Robtek-Gruppe-6/semesterproject_4_6/Time_constant_pan.png

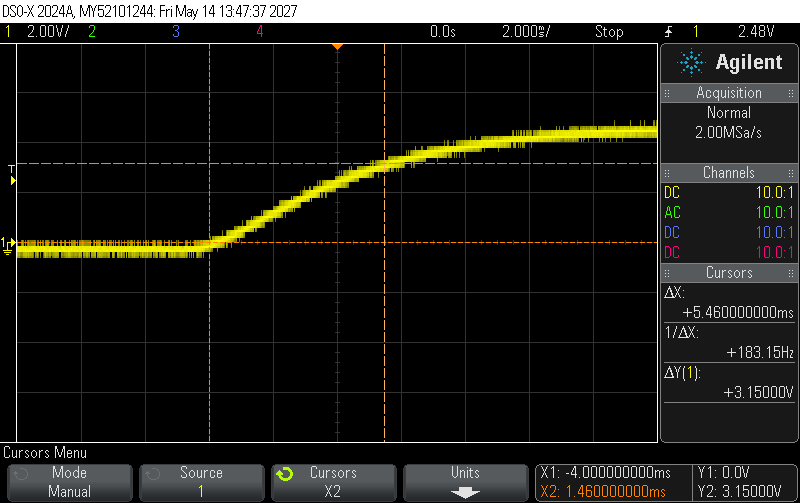
Time_constant_pan.png
