Robtek-Gruppe-6/semesterproject_4_6/Matlab/pid_tests/pan_nopid.png

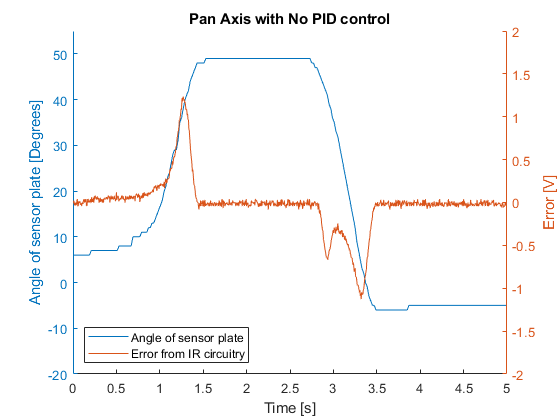
Matlab/pid_tests/pan_nopid.png
