Robtek-Gruppe-6/semesterproject_4_6/Matlab/pid_tests/pan_pid.png

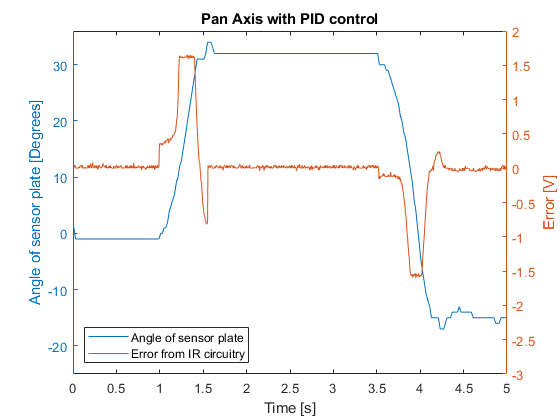
Matlab/pid_tests/pan_pid.png
