Robtek-Gruppe-6/semesterproject_4_6/Matlab/pid_tests/tilt_pid.png

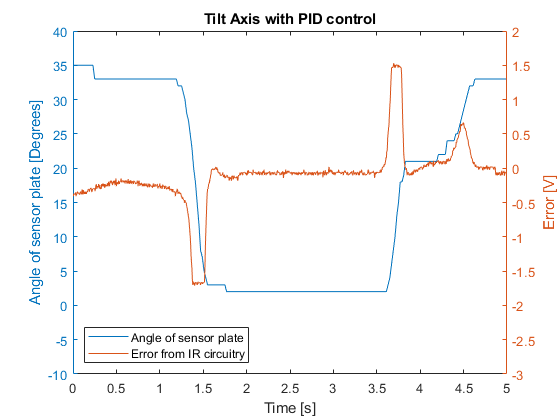
Matlab/pid_tests/tilt_pid.png
