Robtek-Gruppe-6/semesterproject_4_6/Electronics/adder-diff-circuit.kicad_sch

## KiCad design Electronics/adder-diff-circuit.kicad_sch (2025-03-26)

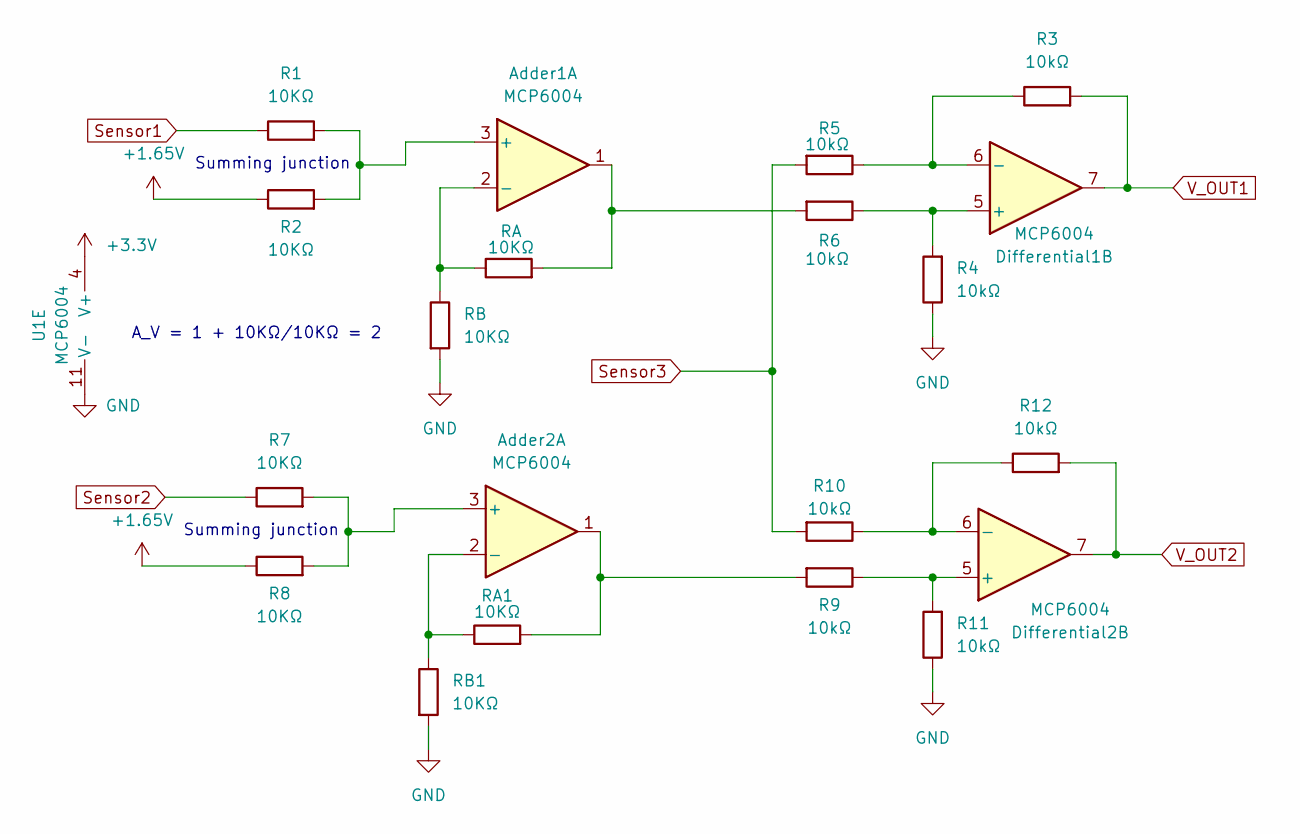
[picture p18: schematic adder-diff-circuit.kicad_sch]

Parts:
Adder1, Adder2: MCP6004
Differential1, Differential2: MCP6004
R1, R2, R7, R8: 10KΩ
R3, R4, R5, R6, R9, R10, R11, R12: 10kΩ
RA, RA1: 10KΩ
RB, RB1: 10KΩ
U1: MCP6004

Connections:
+1.65V: R2.1, R8.1
+3.3V: U1.4 (V+)
GND: R4.1, R11.1, RB.2, RB1.2, U1.11 (V-)
unnamed: Adder1.1, R6.2, RA.2
unnamed: Adder1.2 (-), RA.1, RB.1
unnamed: Adder1.3 (+), R1.2, R2.2
unnamed: Adder2.1, R9.2, RA1.2
unnamed: Adder2.2 (-), RA1.1, RB1.1
unnamed: Adder2.3 (+), R7.2, R8.2
unnamed: Differential1.5 (+), R4.2, R6.1
unnamed: Differential1.6 (-), R3.1, R5.1
unnamed: Differential2.5 (+), R9.1, R11.2
unnamed: Differential2.6 (-), R10.1, R12.1
Sensor1: R1.1
Sensor2: R7.1
Sensor3: R5.2, R10.2
V_OUT1: Differential1.7, R3.2
V_OUT2: Differential2.7, R12.2

Notes on the sheet:
A_V = 1 + 10KΩ/10KΩ = 2
Summing junction
