Robtek-Gruppe-6/semesterproject_4_6/FPGA/sources/home_handler.vhd

----------------------------------------------------------------------------------
-- Company: 
-- Engineer: 
-- 
-- Create Date: 23.04.2025 10:33:51
-- Design Name: 
-- Module Name: home_handler - Behavioral
-- Project Name: 
-- Target Devices: 
-- Tool Versions: 
-- Description: 
-- 
-- Dependencies: 
-- 
-- Revision:
-- Revision 0.01 - File Created
-- Additional Comments:
-- 
----------------------------------------------------------------------------------


library IEEE;
use IEEE.STD_LOGIC_1164.ALL;

-- Uncomment the following library declaration if using
-- arithmetic functions with Signed or Unsigned values
use IEEE.NUMERIC_STD.ALL;

-- Uncomment the following library declaration if instantiating
-- any Xilinx leaf cells in this code.
--library UNISIM;
--use UNISIM.VComponents.all;

entity home_handler is
    Port ( clk : in STD_LOGIC;
           en : in STD_LOGIC;
           home, hall_1, hall_2 : in STD_LOGIC;
           rst : in STD_LOGIC;
           motor1,motor2 : out STD_LOGIC_VECTOR (1 downto 0));
end home_handler;

architecture Behavioral of home_handler is
    type STATE_TYPE is (START, MOTOR1_HOME, MOTOR2_HOME);
    signal current_state, next_state    : STATE_TYPE;
    signal counter  : INTEGER range 0 to 5_000_000 := 0; --adjust max based on clock speed
    signal pwm_sig  : STD_LOGIC := '0';
    signal pwm_counter  : INTEGER range 0 to 1000 := 0; --1000 = 100% 55 = 5.5%
    
begin
    pwm_logic : process (clk)
    begin
        if (rising_edge(clk) and en = '1') then
            pwm_counter <= pwm_counter + 1;
            
            if pwm_counter < 50 then -- 5% duty cycle
                pwm_sig <= '1';
            else
                pwm_sig <= '0';
            end if;
            
            if pwm_counter >= 1000 then
                pwm_counter <= 0;
            end if;
        end if;
    end process;

    current_state_logic : process (clk, rst)
    begin
        if (rst = '1') then -- asyncs reset to stop the motors where they are
            current_state <= START;
        elsif (rising_edge(clk) and en = '1') then
            current_state <= next_state;
        end if;
    end process;
-------------------------------------------------------------------------------  
    next_state_logic : process(current_state, home, hall_1, hall_2)
    begin
        case current_state is
            when START =>
                if (home = '1') then
                    next_state <= MOTOR1_HOME;
                else
                    next_state <= START;
                end if;
                
            when MOTOR1_HOME =>
                if (hall_1 = '1') then
                    next_state <= MOTOR2_HOME;
                else
                    next_state <= MOTOR1_HOME;
                end if;
                    
            when MOTOR2_HOME =>
                if (hall_2 = '1') then
                    next_state <= START;
                else
                    next_state <= MOTOR2_HOME;
                end if;
                
            when others =>
                next_state <= START;
        end case;
    end process next_state_logic;
 ------------------------------------------------------------------------------------------------   
    output_logic : process(clk, rst)
    begin 
        if (rst = '1') then
            -- logic for reseting
            motor1 <= (others => '0');
            motor2 <= (others => '0');
        elsif rising_edge(clk) then
            
            if current_state = MOTOR1_HOME then
                --Logic to home motor 1
                motor1 <= '0' & pwm_sig; -- Forward
                
                if (counter < 5000000) then
                    counter <= counter + 1;
                else 
                    motor1 <= pwm_sig & '0';
                end if;
                
            elsif current_state = MOTOR2_home then
                -- Logic to home motor 2
                motor2 <= '0' & pwm_sig; -- Forward
            
            else
                -- Logic for start state
                motor1 <= (others => '0');
                motor2 <= (others => '0');
            end if;
        end if;
    end process;
            
end Behavioral;
