Robtek-Gruppe-6/semesterproject_4_6/Microcontroller/status_led.c

/*****************************************************************************
* University of Southern Denmark
* Embedded C Programming (ECP)
*
* MODULENAME.: status_led.c
*
* PROJECT....: SEMESTERPROJECT
*
* DESCRIPTION: See module specification file (.h-file).
*
* Change Log:
******************************************************************************
* Date    Id    Change
* YYMMDD
* --------------------
* 050128  KA    Module created.
*
*****************************************************************************/

/***************************** Include files *******************************/
#include <stdint.h>
#include "tm4c123gh6pm.h"
#include "FreeRTOS.h"
#include "Task.h"
#include "queue.h"
#include "semphr.h"
#include "emp_type.h"
#include "status_led.h"

QueueHandle_t xQueue_lcd;
SemaphoreHandle_t xSemaphore_lcd;

/*****************************    Defines    *******************************/
#define PF0		0		// Bit 0

/*****************************   Constants   *******************************/

/*****************************   Variables   *******************************/

/*****************************   Functions   *******************************/

void status_led_init(void)
/*****************************************************************************
*   Input    : 	-
*   Output   : 	-
*   Function : 	
*****************************************************************************/
{
  INT8S dummy;
  // Enable the GPIO port that is used for the on-board LED.
  SYSCTL_RCGC2_R |= SYSCTL_RCGC2_GPIOD;

  // Do a dummy read to insert a few cycles after enabling the peripheral.
  dummy = SYSCTL_RCGC2_R;

  GPIO_PORTD_DIR_R |= 0x40;
  GPIO_PORTD_DEN_R |= 0x40;
}


void status_led_task(void *pvParameters)
{
	
	status_led_init();
	while(1)
	{
		// Toggle status led
	    GPIO_PORTD_DATA_R ^= 0x40;
		vTaskDelay(500 / portTICK_RATE_MS); // wait 500 ms.
	}
}


/****************************** End Of Module *******************************/
