Robtek-Gruppe-6/semesterproject_4_6/Microcontroller/status_led.h

/*****************************************************************************
* University of Southern Denmark
* Embedded C Programming (ECP)
*
* MODULENAME.: status led.h
*
* PROJECT....: SEMESTERPROJECT
*
* DESCRIPTION: Test.
*
* Change Log:
******************************************************************************
* Date    Id    Change
* YYMMDD
* --------------------
* 100408  KHA    Module created.
*
*****************************************************************************/

#ifndef _STATUS_LED_H
  #define _STATUS_LED_H

/***************************** Include files *******************************/

/*****************************    Defines    *******************************/

/*****************************   Constants   *******************************/

/*****************************   Functions   *******************************/


void status_led_init(void);

void status_led_task(void *pvParameters);


/****************************** End Of Module *******************************/
#endif
