Robtek-Gruppe-6/semesterproject_4_6/FPGA/block_designs/FPGA_Main_task/ip/FPGA_Main_task_SPI_slave_block_0_1/FPGA_Main_task_SPI_slave_block_0_1_sim_netlist.vhdl

-- Copyright 1986-2022 Xilinx, Inc. All Rights Reserved.
-- Copyright 2022-2024 Advanced Micro Devices, Inc. All Rights Reserved.
-- --------------------------------------------------------------------------------
-- Tool Version: Vivado v.2024.2 (win64) Build 5239630 Fri Nov 08 22:35:27 MST 2024
-- Date        : Wed May  7 16:08:22 2025
-- Host        : LAPTOP-FABER running 64-bit major release  (build 9200)
-- Command     : write_vhdl -force -mode funcsim
--               c:/Users/Bluex/Desktop/FPGA_Programming/semesterproject_4_6/FPGA/block_designs/FPGA_Main_task/ip/FPGA_Main_task_SPI_slave_block_0_1/FPGA_Main_task_SPI_slave_block_0_1_sim_netlist.vhdl
-- Design      : FPGA_Main_task_SPI_slave_block_0_1
-- Purpose     : This VHDL netlist is a functional simulation representation of the design and should not be modified or
--               synthesized. This netlist cannot be used for SDF annotated simulation.
-- Device      : xc7z020clg400-1
-- --------------------------------------------------------------------------------
library IEEE;
use IEEE.STD_LOGIC_1164.ALL;
library UNISIM;
use UNISIM.VCOMPONENTS.ALL;
entity FPGA_Main_task_SPI_slave_block_0_1_SPI_slave_block is
  port (
    miso : out STD_LOGIC;
    rx : out STD_LOGIC_VECTOR ( 15 downto 0 );
    ss : in STD_LOGIC;
    rst : in STD_LOGIC;
    read_en : in STD_LOGIC;
    cpha : in STD_LOGIC;
    sck : in STD_LOGIC;
    cpol : in STD_LOGIC;
    tx : in STD_LOGIC_VECTOR ( 15 downto 0 );
    mosi : in STD_LOGIC
  );
  attribute ORIG_REF_NAME : string;
  attribute ORIG_REF_NAME of FPGA_Main_task_SPI_slave_block_0_1_SPI_slave_block : entity is "SPI_slave_block";
end FPGA_Main_task_SPI_slave_block_0_1_SPI_slave_block;

architecture STRUCTURE of FPGA_Main_task_SPI_slave_block_0_1_SPI_slave_block is
  signal \active_bit[16]_i_1_n_0\ : STD_LOGIC;
  signal \active_bit[1]_C_i_1_n_0\ : STD_LOGIC;
  signal \active_bit[2]_i_1_n_0\ : STD_LOGIC;
  signal \active_bit_reg[0]_LDC_n_0\ : STD_LOGIC;
  signal \active_bit_reg[0]_P_n_0\ : STD_LOGIC;
  signal \active_bit_reg[1]_C_n_0\ : STD_LOGIC;
  signal \active_bit_reg[1]_LDC_i_1_n_0\ : STD_LOGIC;
  signal \active_bit_reg[1]_LDC_i_2_n_0\ : STD_LOGIC;
  signal \active_bit_reg[1]_LDC_n_0\ : STD_LOGIC;
  signal \active_bit_reg[1]_P_n_0\ : STD_LOGIC;
  signal \active_bit_reg_n_0_[10]\ : STD_LOGIC;
  signal \active_bit_reg_n_0_[11]\ : STD_LOGIC;
  signal \active_bit_reg_n_0_[12]\ : STD_LOGIC;
  signal \active_bit_reg_n_0_[13]\ : STD_LOGIC;
  signal \active_bit_reg_n_0_[14]\ : STD_LOGIC;
  signal \active_bit_reg_n_0_[15]\ : STD_LOGIC;
  signal \active_bit_reg_n_0_[16]\ : STD_LOGIC;
  signal \active_bit_reg_n_0_[2]\ : STD_LOGIC;
  signal \active_bit_reg_n_0_[3]\ : STD_LOGIC;
  signal \active_bit_reg_n_0_[4]\ : STD_LOGIC;
  signal \active_bit_reg_n_0_[5]\ : STD_LOGIC;
  signal \active_bit_reg_n_0_[6]\ : STD_LOGIC;
  signal \active_bit_reg_n_0_[7]\ : STD_LOGIC;
  signal \active_bit_reg_n_0_[8]\ : STD_LOGIC;
  signal \active_bit_reg_n_0_[9]\ : STD_LOGIC;
  signal miso_i_2_n_0 : STD_LOGIC;
  signal p_2_in : STD_LOGIC;
  signal p_3_in : STD_LOGIC_VECTOR ( 15 downto 1 );
  signal rx0 : STD_LOGIC;
  signal rx_reg : STD_LOGIC_VECTOR ( 15 downto 0 );
  signal \rx_reg[15]_i_1__0_n_0\ : STD_LOGIC;
  signal tx_reg : STD_LOGIC_VECTOR ( 15 to 15 );
  signal \tx_reg[10]_C_i_1_n_0\ : STD_LOGIC;
  signal \tx_reg[11]_C_i_1_n_0\ : STD_LOGIC;
  signal \tx_reg[12]_C_i_1_n_0\ : STD_LOGIC;
  signal \tx_reg[13]_C_i_1_n_0\ : STD_LOGIC;
  signal \tx_reg[14]_C_i_1_n_0\ : STD_LOGIC;
  signal \tx_reg[15]_C_i_1_n_0\ : STD_LOGIC;
  signal \tx_reg[1]_C_i_1_n_0\ : STD_LOGIC;
  signal \tx_reg[2]_C_i_1_n_0\ : STD_LOGIC;
  signal \tx_reg[3]_C_i_1_n_0\ : STD_LOGIC;
  signal \tx_reg[4]_C_i_1_n_0\ : STD_LOGIC;
  signal \tx_reg[5]_C_i_1_n_0\ : STD_LOGIC;
  signal \tx_reg[6]_C_i_1_n_0\ : STD_LOGIC;
  signal \tx_reg[7]_C_i_1_n_0\ : STD_LOGIC;
  signal \tx_reg[8]_C_i_1_n_0\ : STD_LOGIC;
  signal \tx_reg[9]_C_i_1_n_0\ : STD_LOGIC;
  signal \tx_reg_reg[0]_LDC_i_1_n_0\ : STD_LOGIC;
  signal \tx_reg_reg[0]_LDC_i_2_n_0\ : STD_LOGIC;
  signal \tx_reg_reg[0]_LDC_n_0\ : STD_LOGIC;
  signal \tx_reg_reg[0]_P_n_0\ : STD_LOGIC;
  signal \tx_reg_reg[10]_C_n_0\ : STD_LOGIC;
  signal \tx_reg_reg[10]_LDC_i_1_n_0\ : STD_LOGIC;
  signal \tx_reg_reg[10]_LDC_i_2_n_0\ : STD_LOGIC;
  signal \tx_reg_reg[10]_LDC_n_0\ : STD_LOGIC;
  signal \tx_reg_reg[10]_P_n_0\ : STD_LOGIC;
  signal \tx_reg_reg[11]_C_n_0\ : STD_LOGIC;
  signal \tx_reg_reg[11]_LDC_i_1_n_0\ : STD_LOGIC;
  signal \tx_reg_reg[11]_LDC_i_2_n_0\ : STD_LOGIC;
  signal \tx_reg_reg[11]_LDC_n_0\ : STD_LOGIC;
  signal \tx_reg_reg[11]_P_n_0\ : STD_LOGIC;
  signal \tx_reg_reg[12]_C_n_0\ : STD_LOGIC;
  signal \tx_reg_reg[12]_LDC_i_1_n_0\ : STD_LOGIC;
  signal \tx_reg_reg[12]_LDC_i_2_n_0\ : STD_LOGIC;
  signal \tx_reg_reg[12]_LDC_n_0\ : STD_LOGIC;
  signal \tx_reg_reg[12]_P_n_0\ : STD_LOGIC;
  signal \tx_reg_reg[13]_C_n_0\ : STD_LOGIC;
  signal \tx_reg_reg[13]_LDC_i_1_n_0\ : STD_LOGIC;
  signal \tx_reg_reg[13]_LDC_i_2_n_0\ : STD_LOGIC;
  signal \tx_reg_reg[13]_LDC_n_0\ : STD_LOGIC;
  signal \tx_reg_reg[13]_P_n_0\ : STD_LOGIC;
  signal \tx_reg_reg[14]_C_n_0\ : STD_LOGIC;
  signal \tx_reg_reg[14]_LDC_i_1_n_0\ : STD_LOGIC;
  signal \tx_reg_reg[14]_LDC_i_2_n_0\ : STD_LOGIC;
  signal \tx_reg_reg[14]_LDC_n_0\ : STD_LOGIC;
  signal \tx_reg_reg[14]_P_n_0\ : STD_LOGIC;
  signal \tx_reg_reg[15]_C_n_0\ : STD_LOGIC;
  signal \tx_reg_reg[15]_LDC_i_1_n_0\ : STD_LOGIC;
  signal \tx_reg_reg[15]_LDC_i_2_n_0\ : STD_LOGIC;
  signal \tx_reg_reg[15]_LDC_n_0\ : STD_LOGIC;
  signal \tx_reg_reg[15]_P_n_0\ : STD_LOGIC;
  signal \tx_reg_reg[1]_C_n_0\ : STD_LOGIC;
  signal \tx_reg_reg[1]_LDC_i_1_n_0\ : STD_LOGIC;
  signal \tx_reg_reg[1]_LDC_i_2_n_0\ : STD_LOGIC;
  signal \tx_reg_reg[1]_LDC_n_0\ : STD_LOGIC;
  signal \tx_reg_reg[1]_P_n_0\ : STD_LOGIC;
  signal \tx_reg_reg[2]_C_n_0\ : STD_LOGIC;
  signal \tx_reg_reg[2]_LDC_i_1_n_0\ : STD_LOGIC;
  signal \tx_reg_reg[2]_LDC_i_2_n_0\ : STD_LOGIC;
  signal \tx_reg_reg[2]_LDC_n_0\ : STD_LOGIC;
  signal \tx_reg_reg[2]_P_n_0\ : STD_LOGIC;
  signal \tx_reg_reg[3]_C_n_0\ : STD_LOGIC;
  signal \tx_reg_reg[3]_LDC_i_1_n_0\ : STD_LOGIC;
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
  attribute XILINX_TRANSFORM_PINMAP of \tx_reg_reg[0]_LDC\ : label is "VCC:GE";
  attribute XILINX_LEGACY_PRIM of \tx_reg_reg[10]_LDC\ : label is "LDC";
  attribute XILINX_TRANSFORM_PINMAP of \tx_reg_reg[10]_LDC\ : label is "VCC:GE";
  attribute XILINX_LEGACY_PRIM of \tx_reg_reg[11]_LDC\ : label is "LDC";
  attribute XILINX_TRANSFORM_PINMAP of \tx_reg_reg[11]_LDC\ : label is "VCC:GE";
  attribute XILINX_LEGACY_PRIM of \tx_reg_reg[12]_LDC\ : label is "LDC";
  attribute XILINX_TRANSFORM_PINMAP of \tx_reg_reg[12]_LDC\ : label is "VCC:GE";
  attribute XILINX_LEGACY_PRIM of \tx_reg_reg[13]_LDC\ : label is "LDC";
  attribute XILINX_TRANSFORM_PINMAP of \tx_reg_reg[13]_LDC\ : label is "VCC:GE";
  attribute XILINX_LEGACY_PRIM of \tx_reg_reg[14]_LDC\ : label is "LDC";
  attribute XILINX_TRANSFORM_PINMAP of \tx_reg_reg[14]_LDC\ : label is "VCC:GE";
  attribute XILINX_LEGACY_PRIM of \tx_reg_reg[15]_LDC\ : label is "LDC";
  attribute XILINX_TRANSFORM_PINMAP of \tx_reg_reg[15]_LDC\ : label is "VCC:GE";
  attribute XILINX_LEGACY_PRIM of \tx_reg_reg[1]_LDC\ : label is "LDC";
  attribute XILINX_TRANSFORM_PINMAP of \tx_reg_reg[1]_LDC\ : label is "VCC:GE";
  attribute XILINX_LEGACY_PRIM of \tx_reg_reg[2]_LDC\ : label is "LDC";
  attribute XILINX_TRANSFORM_PINMAP of \tx_reg_reg[2]_LDC\ : label is "VCC:GE";
  attribute XILINX_LEGACY_PRIM of \tx_reg_reg[3]_LDC\ : label is "LDC";
  attribute XILINX_TRANSFORM_PINMAP of \tx_reg_reg[3]_LDC\ : label is "VCC:GE";
  attribute XILINX_LEGACY_PRIM of \tx_reg_reg[4]_LDC\ : label is "LDC";
  attribute XILINX_TRANSFORM_PINMAP of \tx_reg_reg[4]_LDC\ : label is "VCC:GE";
  attribute XILINX_LEGACY_PRIM of \tx_reg_reg[5]_LDC\ : label is "LDC";
  attribute XILINX_TRANSFORM_PINMAP of \tx_reg_reg[5]_LDC\ : label is "VCC:GE";
  attribute XILINX_LEGACY_PRIM of \tx_reg_reg[6]_LDC\ : label is "LDC";
  attribute XILINX_TRANSFORM_PINMAP of \tx_reg_reg[6]_LDC\ : label is "VCC:GE";
  attribute XILINX_LEGACY_PRIM of \tx_reg_reg[7]_LDC\ : label is "LDC";
  attribute XILINX_TRANSFORM_PINMAP of \tx_reg_reg[7]_LDC\ : label is "VCC:GE";
  attribute XILINX_LEGACY_PRIM of \tx_reg_reg[8]_LDC\ : label is "LDC";
  attribute XILINX_TRANSFORM_PINMAP of \tx_reg_reg[8]_LDC\ : label is "VCC:GE";
  attribute XILINX_LEGACY_PRIM of \tx_reg_reg[9]_LDC\ : label is "LDC";
  attribute XILINX_TRANSFORM_PINMAP of \tx_reg_reg[9]_LDC\ : label is "VCC:GE";
begin
\active_bit[16]_i_1\: unisim.vcomponents.LUT2
    generic map(
      INIT => X"E"
    )
        port map (
      I0 => ss,
      I1 => rst,
      O => \active_bit[16]_i_1_n_0\
    );
\active_bit[1]_C_i_1\: unisim.vcomponents.LUT2
    generic map(
      INIT => X"8"
    )
        port map (
      I0 => \active_bit_reg[0]_LDC_n_0\,
      I1 => \active_bit_reg[0]_P_n_0\,
      O => \active_bit[1]_C_i_1_n_0\
    );
\active_bit[2]_i_1\: unisim.vcomponents.LUT3
    generic map(
      INIT => X"B8"
    )
        port map (
      I0 => \active_bit_reg[1]_P_n_0\,
      I1 => \active_bit_reg[1]_LDC_n_0\,
      I2 => \active_bit_reg[1]_C_n_0\,
      O => \active_bit[2]_i_1_n_0\
    );
\active_bit_reg[0]_LDC\: unisim.vcomponents.LDCE
    generic map(
      INIT => '0'
    )
        port map (
      CLR => \active_bit_reg[1]_LDC_i_1_n_0\,
      D => '1',
      G => \active_bit_reg[1]_LDC_i_2_n_0\,
      GE => '1',
      Q => \active_bit_reg[0]_LDC_n_0\
    );
\active_bit_reg[0]_P\: unisim.vcomponents.FDPE
     port map (
      C => miso_i_2_n_0,
      CE => '1',
      D => '0',
      PRE => \active_bit_reg[1]_LDC_i_2_n_0\,
      Q => \active_bit_reg[0]_P_n_0\
    );
\active_bit_reg[10]\: unisim.vcomponents.FDCE
     port map (
      C => miso_i_2_n_0,
      CE => '1',
      CLR => \active_bit[16]_i_1_n_0\,
      D => \active_bit_reg_n_0_[9]\,
      Q => \active_bit_reg_n_0_[10]\
    );
\active_bit_reg[11]\: unisim.vcomponents.FDCE
     port map (
      C => miso_i_2_n_0,
      CE => '1',
      CLR => \active_bit[16]_i_1_n_0\,
      D => \active_bit_reg_n_0_[10]\,
      Q => \active_bit_reg_n_0_[11]\
    );
\active_bit_reg[12]\: unisim.vcomponents.FDCE
     port map (
      C => miso_i_2_n_0,
      CE => '1',
      CLR => \active_bit[16]_i_1_n_0\,
      D => \active_bit_reg_n_0_[11]\,
      Q => \active_bit_reg_n_0_[12]\
    );
\active_bit_reg[13]\: unisim.vcomponents.FDCE
     port map (
      C => miso_i_2_n_0,
      CE => '1',
      CLR => \active_bit[16]_i_1_n_0\,
      D => \active_bit_reg_n_0_[12]\,
      Q => \active_bit_reg_n_0_[13]\
    );
\active_bit_reg[14]\: unisim.vcomponents.FDCE
     port map (
      C => miso_i_2_n_0,
      CE => '1',
      CLR => \active_bit[16]_i_1_n_0\,
      D => \active_bit_reg_n_0_[13]\,
      Q => \active_bit_reg_n_0_[14]\
    );
\active_bit_reg[15]\: unisim.vcomponents.FDCE
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
      INIT => X"B8"
    )
        port map (
      I0 => \tx_reg_reg[6]_P_n_0\,
      I1 => \tx_reg_reg[6]_LDC_n_0\,
      I2 => \tx_reg_reg[6]_C_n_0\,
      O => p_3_in(7)
    );
\tx_reg[8]_C_i_1\: unisim.vcomponents.LUT5
    generic map(
      INIT => X"FFB800B8"
    )
        port map (
      I0 => \tx_reg_reg[7]_P_n_0\,
      I1 => \tx_reg_reg[7]_LDC_n_0\,
      I2 => \tx_reg_reg[7]_C_n_0\,
      I3 => \active_bit_reg_n_0_[16]\,
      I4 => \tx_reg_reg[8]_C_n_0\,
      O => \tx_reg[8]_C_i_1_n_0\
    );
\tx_reg[8]_P_i_1\: unisim.vcomponents.LUT3
    generic map(
      INIT => X"B8"
    )
        port map (
      I0 => \tx_reg_reg[7]_P_n_0\,
      I1 => \tx_reg_reg[7]_LDC_n_0\,
      I2 => \tx_reg_reg[7]_C_n_0\,
      O => p_3_in(8)
    );
\tx_reg[9]_C_i_1\: unisim.vcomponents.LUT5
    generic map(
      INIT => X"FFB800B8"
    )
        port map (
      I0 => \tx_reg_reg[8]_P_n_0\,
      I1 => \tx_reg_reg[8]_LDC_n_0\,
      I2 => \tx_reg_reg[8]_C_n_0\,
      I3 => \active_bit_reg_n_0_[16]\,
      I4 => \tx_reg_reg[9]_C_n_0\,
      O => \tx_reg[9]_C_i_1_n_0\
    );
\tx_reg[9]_P_i_1\: unisim.vcomponents.LUT3
    generic map(
      INIT => X"B8"
    )
        port map (
      I0 => \tx_reg_reg[8]_P_n_0\,
      I1 => \tx_reg_reg[8]_LDC_n_0\,
      I2 => \tx_reg_reg[8]_C_n_0\,
      O => p_3_in(9)
    );
\tx_reg_reg[0]_LDC\: unisim.vcomponents.LDCE
    generic map(
      INIT => '0'
    )
        port map (
      CLR => \tx_reg_reg[0]_LDC_i_2_n_0\,
      D => '1',
      G => \tx_reg_reg[0]_LDC_i_1_n_0\,
      GE => '1',
      Q => \tx_reg_reg[0]_LDC_n_0\
    );
\tx_reg_reg[0]_LDC_i_1\: unisim.vcomponents.LUT3
    generic map(
      INIT => X"40"
    )
        port map (
      I0 => rst,
      I1 => ss,
      I2 => tx(0),
      O => \tx_reg_reg[0]_LDC_i_1_n_0\
    );
\tx_reg_reg[0]_LDC_i_2\: unisim.vcomponents.LUT3
    generic map(
      INIT => X"AE"
    )
        port map (
      I0 => rst,
      I1 => ss,
      I2 => tx(0),
      O => \tx_reg_reg[0]_LDC_i_2_n_0\
    );
\tx_reg_reg[0]_P\: unisim.vcomponents.FDPE
     port map (
      C => miso_i_2_n_0,
      CE => p_2_in,
      D => '0',
      PRE => \tx_reg_reg[0]_LDC_i_1_n_0\,
      Q => \tx_reg_reg[0]_P_n_0\
    );
\tx_reg_reg[10]_C\: unisim.vcomponents.FDCE
     port map (
      C => miso_i_2_n_0,
      CE => '1',
      CLR => \tx_reg_reg[10]_LDC_i_2_n_0\,
      D => \tx_reg[10]_C_i_1_n_0\,
      Q => \tx_reg_reg[10]_C_n_0\
    );
\tx_reg_reg[10]_LDC\: unisim.vcomponents.LDCE
    generic map(
      INIT => '0'
    )
        port map (
      CLR => \tx_reg_reg[10]_LDC_i_2_n_0\,
      D => '1',
      G => \tx_reg_reg[10]_LDC_i_1_n_0\,
      GE => '1',
      Q => \tx_reg_reg[10]_LDC_n_0\
    );
\tx_reg_reg[10]_LDC_i_1\: unisim.vcomponents.LUT3
    generic map(
      INIT => X"40"
    )
        port map (
      I0 => rst,
      I1 => ss,
      I2 => tx(10),
      O => \tx_reg_reg[10]_LDC_i_1_n_0\
    );
\tx_reg_reg[10]_LDC_i_2\: unisim.vcomponents.LUT3
    generic map(
      INIT => X"AE"
    )
        port map (
      I0 => rst,
      I1 => ss,
      I2 => tx(10),
      O => \tx_reg_reg[10]_LDC_i_2_n_0\
    );
\tx_reg_reg[10]_P\: unisim.vcomponents.FDPE
     port map (
      C => miso_i_2_n_0,
      CE => p_2_in,
      D => p_3_in(10),
      PRE => \tx_reg_reg[10]_LDC_i_1_n_0\,
      Q => \tx_reg_reg[10]_P_n_0\
    );
\tx_reg_reg[11]_C\: unisim.vcomponents.FDCE
     port map (
      C => miso_i_2_n_0,
      CE => '1',
      CLR => \tx_reg_reg[11]_LDC_i_2_n_0\,
      D => \tx_reg[11]_C_i_1_n_0\,
      Q => \tx_reg_reg[11]_C_n_0\
    );
\tx_reg_reg[11]_LDC\: unisim.vcomponents.LDCE
    generic map(
      INIT => '0'
    )
        port map (
      CLR => \tx_reg_reg[11]_LDC_i_2_n_0\,
      D => '1',
      G => \tx_reg_reg[11]_LDC_i_1_n_0\,
      GE => '1',
      Q => \tx_reg_reg[11]_LDC_n_0\
    );
\tx_reg_reg[11]_LDC_i_1\: unisim.vcomponents.LUT3
    generic map(
      INIT => X"40"
    )
        port map (
      I0 => rst,
      I1 => ss,
      I2 => tx(11),
      O => \tx_reg_reg[11]_LDC_i_1_n_0\
    );
\tx_reg_reg[11]_LDC_i_2\: unisim.vcomponents.LUT3
    generic map(
      INIT => X"AE"
    )
        port map (
      I0 => rst,
      I1 => ss,
      I2 => tx(11),
      O => \tx_reg_reg[11]_LDC_i_2_n_0\
    );
\tx_reg_reg[11]_P\: unisim.vcomponents.FDPE
     port map (
      C => miso_i_2_n_0,
      CE => p_2_in,
      D => p_3_in(11),
      PRE => \tx_reg_reg[11]_LDC_i_1_n_0\,
      Q => \tx_reg_reg[11]_P_n_0\
    );
\tx_reg_reg[12]_C\: unisim.vcomponents.FDCE
     port map (
      C => miso_i_2_n_0,
      CE => '1',
      CLR => \tx_reg_reg[12]_LDC_i_2_n_0\,
      D => \tx_reg[12]_C_i_1_n_0\,
      Q => \tx_reg_reg[12]_C_n_0\
    );
\tx_reg_reg[12]_LDC\: unisim.vcomponents.LDCE
    generic map(
      INIT => '0'
    )
        port map (
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
      D => \tx_reg[9]_C_i_1_n_0\,
      Q => \tx_reg_reg[9]_C_n_0\
    );
\tx_reg_reg[9]_LDC\: unisim.vcomponents.LDCE
    generic map(
      INIT => '0'
    )
        port map (
      CLR => \tx_reg_reg[9]_LDC_i_2_n_0\,
      D => '1',
      G => \tx_reg_reg[9]_LDC_i_1_n_0\,
      GE => '1',
      Q => \tx_reg_reg[9]_LDC_n_0\
    );
\tx_reg_reg[9]_LDC_i_1\: unisim.vcomponents.LUT3
    generic map(
      INIT => X"40"
    )
        port map (
      I0 => rst,
      I1 => ss,
      I2 => tx(9),
      O => \tx_reg_reg[9]_LDC_i_1_n_0\
    );
\tx_reg_reg[9]_LDC_i_2\: unisim.vcomponents.LUT3
    generic map(
      INIT => X"AE"
    )
        port map (
      I0 => rst,
      I1 => ss,
      I2 => tx(9),
      O => \tx_reg_reg[9]_LDC_i_2_n_0\
    );
\tx_reg_reg[9]_P\: unisim.vcomponents.FDPE
     port map (
      C => miso_i_2_n_0,
      CE => p_2_in,
      D => p_3_in(9),
      PRE => \tx_reg_reg[9]_LDC_i_1_n_0\,
      Q => \tx_reg_reg[9]_P_n_0\
    );
end STRUCTURE;
library IEEE;
use IEEE.STD_LOGIC_1164.ALL;
library UNISIM;
use UNISIM.VCOMPONENTS.ALL;
entity FPGA_Main_task_SPI_slave_block_0_1 is
  port (
    cpol : in STD_LOGIC;
    cpha : in STD_LOGIC;
    sck : in STD_LOGIC;
    ss : in STD_LOGIC;
    mosi : in STD_LOGIC;
    miso : out STD_LOGIC;
    read_en : in STD_LOGIC;
    tx : in STD_LOGIC_VECTOR ( 15 downto 0 );
    rx : out STD_LOGIC_VECTOR ( 15 downto 0 );
    busy : out STD_LOGIC;
    rst : in STD_LOGIC
  );
  attribute NotValidForBitStream : boolean;
  attribute NotValidForBitStream of FPGA_Main_task_SPI_slave_block_0_1 : entity is true;
  attribute CHECK_LICENSE_TYPE : string;
  attribute CHECK_LICENSE_TYPE of FPGA_Main_task_SPI_slave_block_0_1 : entity is "FPGA_Main_task_SPI_slave_block_0_1,SPI_slave_block,{}";
  attribute downgradeipidentifiedwarnings : string;
  attribute downgradeipidentifiedwarnings of FPGA_Main_task_SPI_slave_block_0_1 : entity is "yes";
  attribute ip_definition_source : string;
  attribute ip_definition_source of FPGA_Main_task_SPI_slave_block_0_1 : entity is "module_ref";
  attribute x_core_info : string;
  attribute x_core_info of FPGA_Main_task_SPI_slave_block_0_1 : entity is "SPI_slave_block,Vivado 2024.2";
end FPGA_Main_task_SPI_slave_block_0_1;

architecture STRUCTURE of FPGA_Main_task_SPI_slave_block_0_1 is
  attribute x_interface_info : string;
  attribute x_interface_info of rst : signal is "xilinx.com:signal:reset:1.0 rst RST";
  attribute x_interface_mode : string;
  attribute x_interface_mode of rst : signal is "slave rst";
  attribute x_interface_parameter : string;
  attribute x_interface_parameter of rst : signal is "XIL_INTERFACENAME rst, POLARITY ACTIVE_LOW, INSERT_VIP 0";
begin
U0: entity work.FPGA_Main_task_SPI_slave_block_0_1_SPI_slave_block
     port map (
      cpha => cpha,
      cpol => cpol,
      miso => miso,
      mosi => mosi,
      read_en => read_en,
      rst => rst,
      rx(15 downto 0) => rx(15 downto 0),
      sck => sck,
      ss => ss,
      tx(15 downto 0) => tx(15 downto 0)
    );
busy_INST_0: unisim.vcomponents.LUT1
    generic map(
      INIT => X"1"
    )
        port map (
      I0 => ss,
      O => busy
    );
end STRUCTURE;
