Robtek-Gruppe-6/semesterproject_4_6/FPGA/block_designs/FPGA_Main_task/ip/FPGA_Main_task_clock_divider_0_0/FPGA_Main_task_clock_divider_0_0_sim_netlist.vhdl

-- Copyright 1986-2022 Xilinx, Inc. All Rights Reserved.
-- Copyright 2022-2024 Advanced Micro Devices, Inc. All Rights Reserved.
-- --------------------------------------------------------------------------------
-- Tool Version: Vivado v.2024.2 (win64) Build 5239630 Fri Nov 08 22:35:27 MST 2024
-- Date        : Wed May  7 16:54:13 2025
-- Host        : LAPTOP-FABER running 64-bit major release  (build 9200)
-- Command     : write_vhdl -force -mode funcsim
--               c:/Users/Bluex/Desktop/FPGA_Programming/semesterproject_4_6/FPGA/block_designs/FPGA_Main_task/ip/FPGA_Main_task_clock_divider_0_0/FPGA_Main_task_clock_divider_0_0_sim_netlist.vhdl
-- Design      : FPGA_Main_task_clock_divider_0_0
-- Purpose     : This VHDL netlist is a functional simulation representation of the design and should not be modified or
--               synthesized. This netlist cannot be used for SDF annotated simulation.
-- Device      : xc7z020clg400-1
-- --------------------------------------------------------------------------------
library IEEE;
use IEEE.STD_LOGIC_1164.ALL;
library UNISIM;
use UNISIM.VCOMPONENTS.ALL;
entity FPGA_Main_task_clock_divider_0_0_clock_divider is
  port (
    clk_out : out STD_LOGIC;
    en : in STD_LOGIC;
    clk : in STD_LOGIC;
    rst : in STD_LOGIC
  );
  attribute ORIG_REF_NAME : string;
  attribute ORIG_REF_NAME of FPGA_Main_task_clock_divider_0_0_clock_divider : entity is "clock_divider";
end FPGA_Main_task_clock_divider_0_0_clock_divider;

architecture STRUCTURE of FPGA_Main_task_clock_divider_0_0_clock_divider is
  signal clk_out_i_2_n_0 : STD_LOGIC;
  signal cnt : STD_LOGIC_VECTOR ( 6 downto 0 );
  signal \cnt[3]_i_2_n_0\ : STD_LOGIC;
  signal \cnt[5]_i_2_n_0\ : STD_LOGIC;
  signal \cnt_reg_n_0_[0]\ : STD_LOGIC;
  signal \cnt_reg_n_0_[1]\ : STD_LOGIC;
  signal \cnt_reg_n_0_[2]\ : STD_LOGIC;
  signal \cnt_reg_n_0_[3]\ : STD_LOGIC;
  signal \cnt_reg_n_0_[4]\ : STD_LOGIC;
  signal \cnt_reg_n_0_[5]\ : STD_LOGIC;
  signal \cnt_reg_n_0_[6]\ : STD_LOGIC;
  signal p_0_in : STD_LOGIC;
  signal plusOp : STD_LOGIC_VECTOR ( 6 downto 1 );
  signal \plusOp_carry__0_n_1\ : STD_LOGIC;
  signal \plusOp_carry__0_n_3\ : STD_LOGIC;
  signal plusOp_carry_n_0 : STD_LOGIC;
  signal plusOp_carry_n_1 : STD_LOGIC;
  signal plusOp_carry_n_2 : STD_LOGIC;
  signal plusOp_carry_n_3 : STD_LOGIC;
  signal \NLW_plusOp_carry__0_CO_UNCONNECTED\ : STD_LOGIC_VECTOR ( 3 downto 1 );
  signal \NLW_plusOp_carry__0_O_UNCONNECTED\ : STD_LOGIC_VECTOR ( 3 downto 2 );
  attribute SOFT_HLUTNM : string;
  attribute SOFT_HLUTNM of clk_out_i_1 : label is "soft_lutpair0";
  attribute SOFT_HLUTNM of \cnt[0]_i_1\ : label is "soft_lutpair2";
  attribute SOFT_HLUTNM of \cnt[1]_i_1\ : label is "soft_lutpair2";
  attribute SOFT_HLUTNM of \cnt[2]_i_1\ : label is "soft_lutpair1";
  attribute SOFT_HLUTNM of \cnt[3]_i_1\ : label is "soft_lutpair1";
  attribute SOFT_HLUTNM of \cnt[4]_i_1\ : label is "soft_lutpair3";
  attribute SOFT_HLUTNM of \cnt[5]_i_1\ : label is "soft_lutpair3";
  attribute SOFT_HLUTNM of \cnt[6]_i_1\ : label is "soft_lutpair0";
begin
clk_out_i_1: unisim.vcomponents.LUT5
    generic map(
      INIT => X"DDDDEEDF"
    )
        port map (
      I0 => plusOp(6),
      I1 => \plusOp_carry__0_n_1\,
      I2 => \cnt_reg_n_0_[0]\,
      I3 => plusOp(1),
      I4 => clk_out_i_2_n_0,
      O => p_0_in
    );
clk_out_i_2: unisim.vcomponents.LUT4
    generic map(
      INIT => X"7FFF"
    )
        port map (
      I0 => plusOp(3),
      I1 => plusOp(2),
      I2 => plusOp(5),
      I3 => plusOp(4),
      O => clk_out_i_2_n_0
    );
clk_out_reg: unisim.vcomponents.FDCE
     port map (
      C => clk,
      CE => en,
      CLR => rst,
      D => p_0_in,
      Q => clk_out
    );
\cnt[0]_i_1\: unisim.vcomponents.LUT4
    generic map(
      INIT => X"0045"
    )
        port map (
      I0 => \cnt_reg_n_0_[0]\,
      I1 => clk_out_i_2_n_0,
      I2 => plusOp(6),
      I3 => \plusOp_carry__0_n_1\,
      O => cnt(0)
    );
\cnt[1]_i_1\: unisim.vcomponents.LUT4
    generic map(
      INIT => X"008A"
    )
        port map (
      I0 => plusOp(1),
      I1 => clk_out_i_2_n_0,
      I2 => plusOp(6),
      I3 => \plusOp_carry__0_n_1\,
      O => cnt(1)
    );
\cnt[2]_i_1\: unisim.vcomponents.LUT4
    generic map(
      INIT => X"008A"
    )
        port map (
      I0 => plusOp(2),
      I1 => \cnt[3]_i_2_n_0\,
      I2 => plusOp(3),
      I3 => \plusOp_carry__0_n_1\,
      O => cnt(2)
    );
\cnt[3]_i_1\: unisim.vcomponents.LUT4
    generic map(
      INIT => X"008A"
    )
        port map (
      I0 => plusOp(3),
      I1 => \cnt[3]_i_2_n_0\,
      I2 => plusOp(2),
      I3 => \plusOp_carry__0_n_1\,
      O => cnt(3)
    );
\cnt[3]_i_2\: unisim.vcomponents.LUT5
    generic map(
      INIT => X"5DFFFFFF"
    )
        port map (
      I0 => plusOp(6),
      I1 => \cnt_reg_n_0_[0]\,
      I2 => plusOp(1),
      I3 => plusOp(5),
      I4 => plusOp(4),
      O => \cnt[3]_i_2_n_0\
    );
\cnt[4]_i_1\: unisim.vcomponents.LUT4
    generic map(
      INIT => X"008A"
    )
        port map (
      I0 => plusOp(4),
      I1 => \cnt[5]_i_2_n_0\,
      I2 => plusOp(5),
      I3 => \plusOp_carry__0_n_1\,
      O => cnt(4)
    );
\cnt[5]_i_1\: unisim.vcomponents.LUT4
    generic map(
      INIT => X"008A"
    )
        port map (
      I0 => plusOp(5),
      I1 => \cnt[5]_i_2_n_0\,
      I2 => plusOp(4),
      I3 => \plusOp_carry__0_n_1\,
      O => cnt(5)
    );
\cnt[5]_i_2\: unisim.vcomponents.LUT5
    generic map(
      INIT => X"5DFFFFFF"
    )
        port map (
      I0 => plusOp(6),
      I1 => \cnt_reg_n_0_[0]\,
      I2 => plusOp(1),
      I3 => plusOp(3),
      I4 => plusOp(2),
      O => \cnt[5]_i_2_n_0\
    );
\cnt[6]_i_1\: unisim.vcomponents.LUT5
    generic map(
      INIT => X"0000AA20"
    )
        port map (
      I0 => plusOp(6),
      I1 => plusOp(1),
      I2 => \cnt_reg_n_0_[0]\,
      I3 => clk_out_i_2_n_0,
      I4 => \plusOp_carry__0_n_1\,
      O => cnt(6)
    );
\cnt_reg[0]\: unisim.vcomponents.FDCE
    generic map(
      INIT => '0'
    )
        port map (
      C => clk,
      CE => en,
      CLR => rst,
      D => cnt(0),
      Q => \cnt_reg_n_0_[0]\
    );
\cnt_reg[1]\: unisim.vcomponents.FDCE
    generic map(
      INIT => '0'
    )
        port map (
      C => clk,
      CE => en,
      CLR => rst,
      D => cnt(1),
      Q => \cnt_reg_n_0_[1]\
    );
\cnt_reg[2]\: unisim.vcomponents.FDCE
    generic map(
      INIT => '0'
    )
        port map (
      C => clk,
      CE => en,
      CLR => rst,
      D => cnt(2),
      Q => \cnt_reg_n_0_[2]\
    );
\cnt_reg[3]\: unisim.vcomponents.FDCE
    generic map(
      INIT => '0'
    )
        port map (
      C => clk,
      CE => en,
      CLR => rst,
      D => cnt(3),
      Q => \cnt_reg_n_0_[3]\
    );
\cnt_reg[4]\: unisim.vcomponents.FDCE
    generic map(
      INIT => '0'
    )
        port map (
      C => clk,
      CE => en,
      CLR => rst,
      D => cnt(4),
      Q => \cnt_reg_n_0_[4]\
    );
\cnt_reg[5]\: unisim.vcomponents.FDCE
    generic map(
      INIT => '0'
    )
        port map (
      C => clk,
      CE => en,
      CLR => rst,
      D => cnt(5),
      Q => \cnt_reg_n_0_[5]\
    );
\cnt_reg[6]\: unisim.vcomponents.FDCE
    generic map(
      INIT => '0'
    )
        port map (
      C => clk,
      CE => en,
      CLR => rst,
      D => cnt(6),
      Q => \cnt_reg_n_0_[6]\
    );
plusOp_carry: unisim.vcomponents.CARRY4
     port map (
      CI => '0',
      CO(3) => plusOp_carry_n_0,
      CO(2) => plusOp_carry_n_1,
      CO(1) => plusOp_carry_n_2,
      CO(0) => plusOp_carry_n_3,
      CYINIT => \cnt_reg_n_0_[0]\,
      DI(3 downto 0) => B"0000",
      O(3 downto 0) => plusOp(4 downto 1),
      S(3) => \cnt_reg_n_0_[4]\,
      S(2) => \cnt_reg_n_0_[3]\,
      S(1) => \cnt_reg_n_0_[2]\,
      S(0) => \cnt_reg_n_0_[1]\
    );
\plusOp_carry__0\: unisim.vcomponents.CARRY4
     port map (
      CI => plusOp_carry_n_0,
      CO(3) => \NLW_plusOp_carry__0_CO_UNCONNECTED\(3),
      CO(2) => \plusOp_carry__0_n_1\,
      CO(1) => \NLW_plusOp_carry__0_CO_UNCONNECTED\(1),
      CO(0) => \plusOp_carry__0_n_3\,
      CYINIT => '0',
      DI(3 downto 0) => B"0000",
      O(3 downto 2) => \NLW_plusOp_carry__0_O_UNCONNECTED\(3 downto 2),
      O(1 downto 0) => plusOp(6 downto 5),
      S(3 downto 2) => B"01",
      S(1) => \cnt_reg_n_0_[6]\,
      S(0) => \cnt_reg_n_0_[5]\
    );
end STRUCTURE;
library IEEE;
use IEEE.STD_LOGIC_1164.ALL;
library UNISIM;
use UNISIM.VCOMPONENTS.ALL;
entity FPGA_Main_task_clock_divider_0_0 is
  port (
    clk : in STD_LOGIC;
    en : in STD_LOGIC;
    clk_out : out STD_LOGIC;
    rst : in STD_LOGIC
  );
  attribute NotValidForBitStream : boolean;
  attribute NotValidForBitStream of FPGA_Main_task_clock_divider_0_0 : entity is true;
  attribute CHECK_LICENSE_TYPE : string;
  attribute CHECK_LICENSE_TYPE of FPGA_Main_task_clock_divider_0_0 : entity is "FPGA_Main_task_clock_divider_0_0,clock_divider,{}";
  attribute downgradeipidentifiedwarnings : string;
  attribute downgradeipidentifiedwarnings of FPGA_Main_task_clock_divider_0_0 : entity is "yes";
  attribute ip_definition_source : string;
  attribute ip_definition_source of FPGA_Main_task_clock_divider_0_0 : entity is "module_ref";
  attribute x_core_info : string;
  attribute x_core_info of FPGA_Main_task_clock_divider_0_0 : entity is "clock_divider,Vivado 2024.2";
end FPGA_Main_task_clock_divider_0_0;

architecture STRUCTURE of FPGA_Main_task_clock_divider_0_0 is
  attribute x_interface_info : string;
  attribute x_interface_info of clk : signal is "xilinx.com:signal:clock:1.0 clk CLK";
  attribute x_interface_mode : string;
  attribute x_interface_mode of clk : signal is "slave clk";
  attribute x_interface_parameter : string;
  attribute x_interface_parameter of clk : signal is "XIL_INTERFACENAME clk, ASSOCIATED_RESET rst, FREQ_HZ 100000000, FREQ_TOLERANCE_HZ 0, PHASE 0.0, CLK_DOMAIN FPGA_Main_task_clk, INSERT_VIP 0";
  attribute x_interface_info of rst : signal is "xilinx.com:signal:reset:1.0 rst RST";
  attribute x_interface_mode of rst : signal is "slave rst";
  attribute x_interface_parameter of rst : signal is "XIL_INTERFACENAME rst, POLARITY ACTIVE_LOW, INSERT_VIP 0";
begin
U0: entity work.FPGA_Main_task_clock_divider_0_0_clock_divider
     port map (
      clk => clk,
      clk_out => clk_out,
      en => en,
      rst => rst
    );
end STRUCTURE;
